moclei/motion-play/session_data/labeled-data/index.md

| session_id | label | ball_size |
|---|---|---|
|  device-001_19139_selection.csv | a_to_b_medium_edge | 4 inch |
| | | |

## Session location
Files named after the session_id are found in the group1 folder (session_data/labeled-data/group1)
