moclei/motion-play/docs/alt-design/motion-play-alt.rtf

Hoop Ball Detection System
Project Specification Document
Version 1.0 — December 2024
1. Project Overview
This project involves designing and building an electronics system that detects when a soccer ball passes through a suspended hoop, including the direction of travel. The system uses infrared beam-break detection with multiple sensor pairs to ensure reliable detection regardless of where the ball passes through the hoop's cross-section.
1.1 Functional Requirements
• Detect a soccer ball passing through the hoop
• Determine direction of travel (Side A → Side B or Side B → Side A)
• Operate reliably in various lighting conditions (indoor and outdoor)
• Battery-powered with USB-C charging capability
• Visual feedback via integrated display
2. Physical Specifications
2.1 Hoop Construction
Parameter | Value
Material | Flat bar steel
Bar dimensions | 25.4mm wide × 3.4mm thick × 1596mm long
Inner diameter | 500mm
Shape | Perfectly round (bent from flat stock)
Mounting height | Approximately 1 meter (suspended)
2.2 Ball Specifications
Parameter | Value
Type | Size 4 soccer ball
Diameter | 203mm
3. Detection System Design
3.1 Detection Method
The system uses infrared (IR) beam-break detection. IR LEDs emit 940nm light across the hoop diameter, and photodiodes on the opposite side detect the light. When a ball passes through, it blocks the beam, causing the photodiode output to change state.
3.2 Beam Geometry
With a 500mm hoop inner diameter and 203mm ball diameter, geometric analysis confirms that a minimum of three beams are required to guarantee detection regardless of where the ball passes through the hoop plane.
Beam positioning: Due to flex PCB manufacturing constraints (490mm maximum length at JLCPCB), an asymmetric arrangement is used rather than equal 120° spacing:
• IR LEDs positioned at: 0°, 50°, 100° on the hoop
• Sensor pairs positioned at: 180°, 230°, 280° (directly opposite)
• Arc span: 100° ≈ 436mm (within 490mm limit)
This arrangement has been verified geometrically: even at the worst-case position (140°), a ball will intersect at least one beam by approximately 6mm of its radius.
3.3 Direction Detection
Each beam position has two photodiode sensors spaced 25mm apart (the maximum achievable given hoop constraints). When a ball passes through:
1. The first sensor detects the beam break
2. Microseconds later, the second sensor detects the break
3. The order of detection determines direction of travel
The ESP32-S3 uses interrupt-driven timestamping to capture transitions with microsecond precision.
3.4 Timing Analysis
Ball transit times through the hoop plane (203mm travel distance):
Ball Speed | Transit Time | 25mm Sensor Gap
10 m/s (moderate kick) | 20.3ms | 2.5ms
20 m/s (hard kick) | 10.2ms | 1.25ms
30 m/s (professional) | 6.8ms | 0.83ms (833μs)
The selected photodiode (VEMD2020X01) has 100ns response time, providing approximately 8,300 sample opportunities during a 833μs sensor gap transit at maximum speed.
4. Component Selection
4.1 Microcontroller
Parameter | Specification
Module | LilyGO T-Display-S3
Processor | ESP32-S3
Display | Integrated TFT (visible during use)
Key features | Microsecond GPIO interrupt timestamping, multiple PWM channels
4.2 Power System
Parameter | Specification
Module | USB-C power module devkit
Input | USB-C
Output | 5V @ 2.4A via GPIO pins
Battery | 18650 cell (charges while providing power, auto-switchover)
4.3 IR Photodiode Sensors (PROTOTYPE)
Parameter | Specification
Part number | VEMD2020X01
LCSC Part # | C3210968
Manufacturer | Vishay
Type | Silicon PIN photodiode
Peak wavelength | 940nm
Spectral bandwidth | 750nm to 1050nm
Daylight filter | Yes — matched with 830nm to 950nm IR emitters
Half angle | ±15° (narrow, provides natural off-axis rejection)
Response time | 100ns rise/fall
Photocurrent | 12μA typical at 1mW/cm²
Package | 2.3mm × 2.3mm × 2.8mm SMD (gullwing)
Quantity required | 6 (2 per beam × 3 beams)
Stock (LCSC) | 12,235 units
Unit price | $0.364
Selection rationale: The VEMD2020X01 was selected over integrated IR receiver modules (like the IRM-V838M3-C) because those modules have AGC (automatic gain control) that requires burst timing patterns. The burst cycle (~1.2ms) is too slow for reliable direction detection at high ball speeds with 25mm sensor spacing. The photodiode's 100ns response time eliminates this constraint entirely.
4.4 IR LED Emitters (CANDIDATE — PENDING DATASHEET VERIFICATION)
Parameter | Specification
Part number | P2835P1VIRB8G025-940
LCSC Part # | C22466183
Manufacturer | Silverlight
Wavelength | 940nm
Half angle (estimated) | 12°-15°
Beam diameter at 500mm | ~106mm to ~134mm
Package | SMD, 3.5x2.8mm
Quantity required | 3 (1 per beam)
Stock (LCSC) | 230 units
Unit price | $0.1405
Status | Chosen for prototype
5. PCB Architecture
5.1 Board Configuration
The system uses three PCBs manufactured by JLCPCB:
4. Main PCB (rigid): Houses the T-Display-S3 MCU, USB-C power module, 18650 battery holder, ZIF FPC connectors, and supporting circuitry
5. LED Flex PCB: Contains 3× IR LEDs with drive circuits, spans 0° to 100° arc (~436mm)
6. Sensor Flex PCB: Contains 6× photodiodes with detection circuits, spans 180° to 280° arc (~436mm)
5.2 Flex PCB Connections
• ZIF FPC connectors on main PCB
• Flex PCBs conform to hoop's inner curve (250mm radius)
• SMD components only on flex PCBs (reliability on curved surface)
• 0.11mm or 0.2mm polyimide thickness for flexibility
• Stiffeners at component locations and connector ends
5.3 Signal Routing
LED Flex PCB signals: VCC, GND, PWM (can be shared for synchronized pulsing)
Sensor Flex PCB signals: VCC, GND, 6× sensor outputs (one per photodiode)
6. Mechanical Design
6.1 3D Printed Components
Custom 3D-printed clips attach to the 25.4mm × 3.4mm flat steel bar profile:
• Main enclosure clip: Houses main PCB, provides display visibility, battery access
• Flex PCB channel clips: Guide and protect flex PCBs along hoop interior
• Sensor housings: Position photodiodes with 25mm spacing, may include baffles if needed
• LED housings: Position and protect IR LEDs, ensure correct aiming
7. Open Items and Next Steps
7.1 Pending Tasks
7. Photodiode detection circuit design: Design transimpedance amplifier or comparator circuit for converting photodiode current to digital GPIO signal
8. LED drive circuit design: Size current-limiting resistors and MOSFET switches, determine continuous vs. pulsed operation
9. Schematic capture: Create KiCad schematics for all three PCBs
10. PCB layout: Layout main rigid PCB and both flex PCBs in KiCad
11. 3D enclosure design: Model mounting clips and enclosures
12. Firmware development: Implement interrupt-driven detection, direction logic, and display output
7.2 Design Decisions to Finalize
• Continuous vs. modulated (38kHz) LED drive — with photodiodes, continuous may be sufficient and simpler
• Photodiode bias mode — photovoltaic (simpler) vs. reverse-biased (faster, already fast enough)
• Detection circuit topology — simple resistive load vs. transimpedance amplifier vs. comparator
• Main PCB mounting position on hoop
— End of Document —
