moclei/motion-play/hardware/components/t-display-s3/Lilygo-T-display_s3_pinout.webp

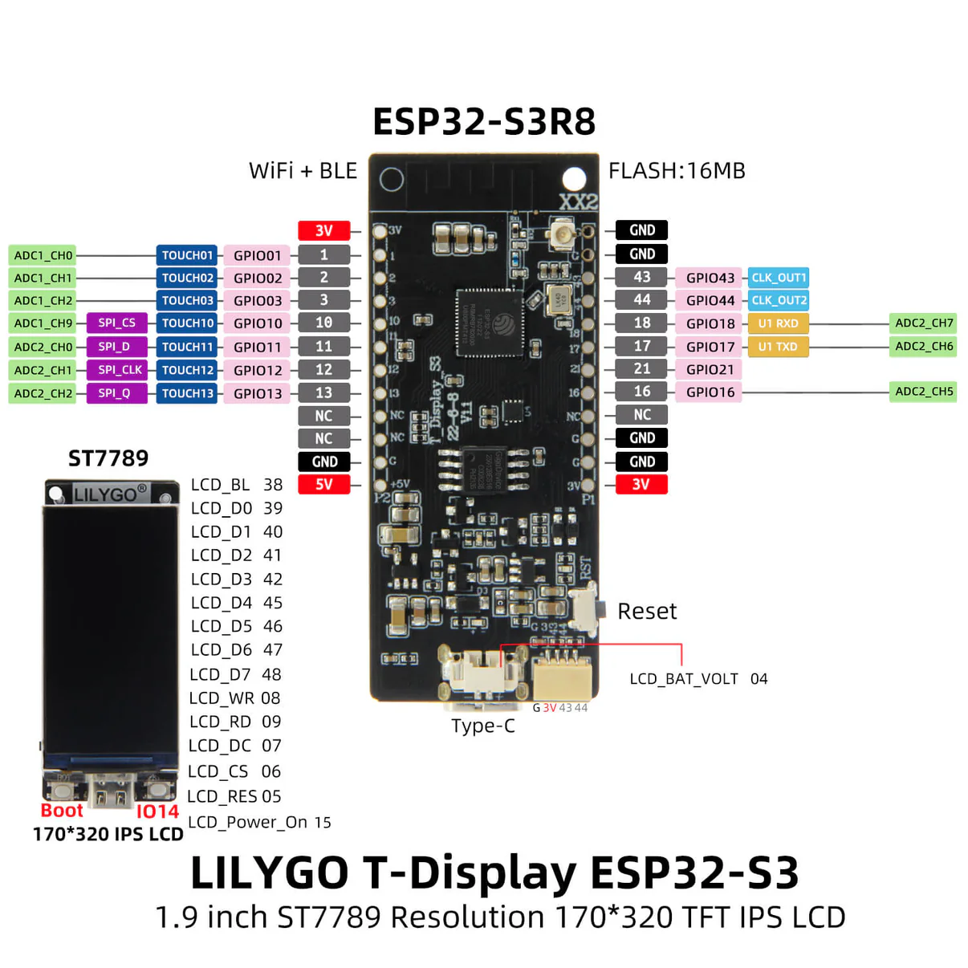
hardware/components/t-display-s3/Lilygo-T-display_s3_pinout.webp
