moclei/motion-play/hardware/components/dweii-power/product listing/Screenshot 2024-12-04 at 5.54.28 PM.png

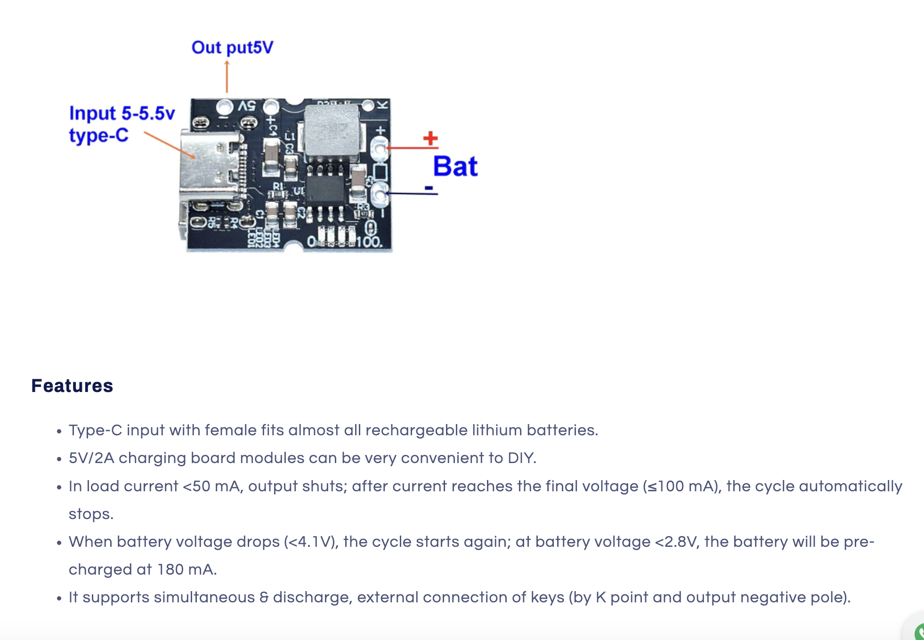
hardware/components/dweii-power/product listing/Screenshot 2024-12-04 at 5.54.28 PM.png
