moclei/motion-play/hardware/components/dweii-power/product listing/Screenshot 2024-12-04 at 5.56.42 PM.png

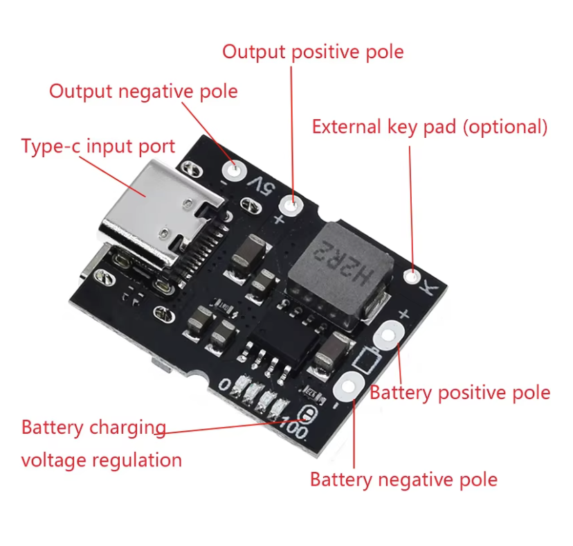
hardware/components/dweii-power/product listing/Screenshot 2024-12-04 at 5.56.42 PM.png
