moclei/motion-play/mechanical/models/router-template/pb_back_router_template_clean.dxf

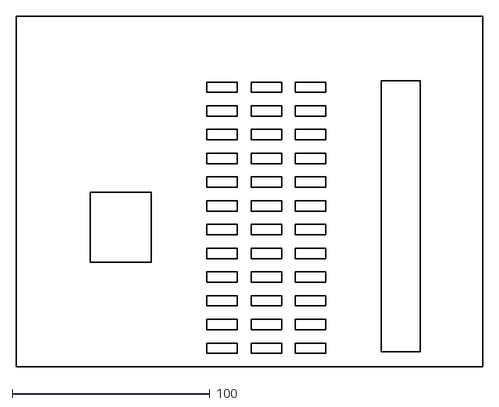
[picture p24: CAD file, 2026-04-03]
mechanical/models/router-template/pb_back_router_template_clean.dxf
235.8 x 177.1
