moclei/motion-play/hardware/components/TPS54331/TPS54331DR.step

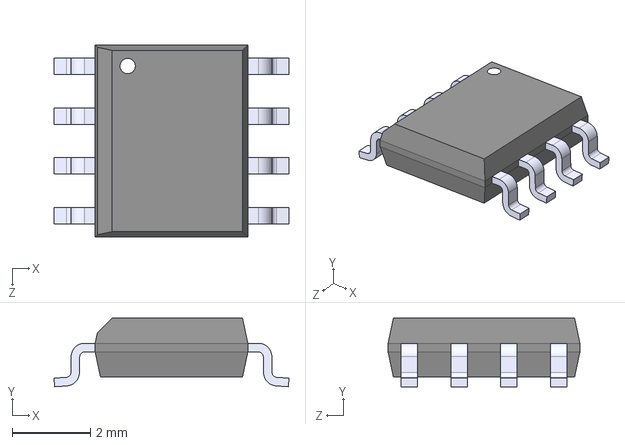
[picture p25: CAD file, 2025-09-09]
hardware/components/TPS54331/TPS54331DR.step
6.00 x 1.75 x 4.90 mm
