moclei/motion-play/hardware/pcb-power-supply/resources/BQ24195RGET/BQ24195RGET.step

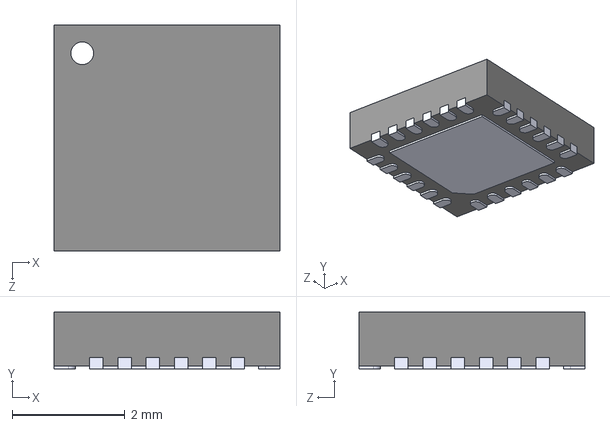
[picture p26: CAD file, 2025-09-03]
hardware/pcb-power-supply/resources/BQ24195RGET/BQ24195RGET.step
4.00 x 1.00 x 4.00 mm
