moclei/motion-play/hardware/components/tca9548a/reference schematic/Adafruit TCA9548A reference schematic.sch

## EAGLE design hardware/components/tca9548a/reference schematic/Adafruit TCA9548A reference schematic.sch (2025-09-03)


Parts:
A0, A1, A2: SOLDERJUMPER; SOLDERJUMPER_ARROW_NOPASTE
C1: 10uF; 0805-NO
FID1, FID3: FIDUCIAL""; FIDUCIAL_1MM
JP1, JP3: HEADER-1X12; 1X12_ROUND
R1, R2, R3, R4, R5: 10K; 0805-NO
R6: 10K; _0805MP
SCLPU: SOLDERJUMPERCLOSED; SOLDERJUMPER_CLOSEDWIRE
SDAPU: SOLDERJUMPERCLOSED; SOLDERJUMPER_CLOSEDWIRE
U1: TCA9548APWR; TSSOP24
U$4, U$5: MOUNTINGHOLE2.5; MOUNTINGHOLE_2.5_PLATED

Connections:
0SCL: JP3.10, U1.5 (SCL0)
0SDA: JP3.9, U1.4 (SDA0)
1SCL: JP3.12, U1.7 (SCL1)
1SDA: JP3.11, U1.6 (SDA1)
2SCL: JP1.2, U1.9 (SCL2)
2SDA: JP1.1, U1.8 (SDA2)
3SCL: JP1.4, U1.11 (SCL3)
3SDA: JP1.3, U1.10 (SDA3)
4SCL: JP1.6, U1.14 (SCL4)
4SDA: JP1.5, U1.13 (SDA4)
5SCL: JP1.8, U1.16 (SCL5)
5SDA: JP1.7, U1.15 (SDA5)
6SCL: JP1.10, U1.18 (SCL6)
6SDA: JP1.9, U1.17 (SDA6)
7SCL: JP1.12, U1.20 (SCL7)
7SDA: JP1.11, U1.19 (SDA7)
A0: A0.1, JP3.6, R5.1, U1.1 (A0)
A1: A1.1, JP3.7, R4.1, U1.2 (A1)
A2: A2.2, JP3.8, R3.1, U1.21 (A2)
GND: C1.2, JP3.2, R3.2, R4.2, R5.2, U1.12 (GND)
INPUTSCL: JP3.4, SCLPU.1, U1.22 (SCL)
INPUTSDA: JP3.3, SDAPU.1, U1.23 (SDA)
unnamed: R2.1, SCLPU.2
unnamed: R1.1, SDAPU.2
RESET: JP3.5, R6.1, U1.3 (#RESET)
VCC: A0.2, A1.2, A2.1, C1.1, JP3.1, R1.2, R2.2, R6.2, U1.24 (VCC)
