moclei/motion-play/firmware/src/components/data/DataTransmitter.cpp

#include "DataTransmitter.h"
#include "../memory/PSRAMAllocator.h"
#include "../calibration/CalibrationData.h"
#include "mbedtls/base64.h"

DataTransmitter::DataTransmitter(MQTTManager *mqtt) : mqttManager(mqtt)
{
    // Constructor
}

// ============================================================================
// Main entry point - routes to correct transmission method
// ============================================================================

bool DataTransmitter::transmitSession(SessionManager &session, const SensorConfiguration *config)
{
    if (session.getSessionType() == SessionType::INTERRUPT_BASED)
    {
        return transmitInterruptSession(session, config);
    }
    else
    {
        return transmitProximitySession(session, config);
    }
}

// ============================================================================
// Proximity Mode Transmission (existing implementation)
// ============================================================================

bool DataTransmitter::transmitBatch(const String &sessionId,
                                    const String &deviceId,
                                    unsigned long startTime,
                                    unsigned long duration,
                                    std::vector<SensorReading, PSRAMAllocator<SensorReading>> &readings,
                                    size_t offset,
                                    size_t count,
                                    const std::vector<SensorMetadata> *sensorMetadata,
                                    const SensorConfiguration *config)
{
    // Create JSON document
    DynamicJsonDocument doc(8192); // 8KB for batch

    doc["session_id"] = sessionId;
    doc["device_id"] = deviceId;
    doc["session_type"] = "proximity";           // Explicit session type
    doc["start_timestamp"] = startTime * 1000UL; // Convert session start from ms to us (consistent with reading timestamps)
    doc["duration_ms"] = duration;
    doc["sample_rate"] = SAMPLE_RATE_HZ;
    doc["batch_offset"] = offset;
    doc["batch_size"] = count;
    doc["timestamp_unit"] = "us"; // Signal to Lambda that timestamps are in microseconds

    // Add sensor metadata AND configuration (only in first batch)
    if (offset == 0 && sensorMetadata != nullptr)
    {
        // Add active sensor list
        JsonArray sensorArray = doc.createNestedArray("active_sensors");

        for (const auto &sensor : *sensorMetadata)
        {
            JsonObject sensorObj = sensorArray.createNestedObject();
            sensorObj["pos"] = sensor.position;
            sensorObj["pcb"] = sensor.pcb_id;
            sensorObj["side"] = sensor.side;
            sensorObj["name"] = sensor.name;
            sensorObj["active"] = sensor.active;
        }

        // Add VCNL4040 configuration parameters
        if (config != nullptr)
        {
            JsonObject configObj = doc.createNestedObject("vcnl4040_config");
            configObj["sample_rate_hz"] = config->sample_rate_hz;
            configObj["led_current"] = config->led_current;
            configObj["integration_time"] = config->integration_time;
            configObj["duty_cycle"] = config->duty_cycle;
            configObj["multi_pulse"] = config->multi_pulse;
            configObj["high_resolution"] = config->high_resolution;
            configObj["read_ambient"] = config->read_ambient;
            configObj["i2c_clock_khz"] = config->i2c_clock_khz;
            configObj["actual_sample_rate_hz"] = config->actual_sample_rate_hz;
        }

        // Add calibration metadata if available
        if (deviceCalibration.isValid())
        {
            JsonObject calObj = doc.createNestedObject("calibration");
            calObj["valid"] = true;
            calObj["timestamp"] = deviceCalibration.timestamp;
            calObj["multi_pulse"] = deviceCalibration.multi_pulse;
            calObj["integration_time"] = deviceCalibration.integration_time;

            JsonArray thresholds = calObj.createNestedArray("thresholds");
            for (int i = 0; i < CALIBRATION_NUM_PCBS; i++)
            {
                JsonObject pcbCal = thresholds.createNestedObject();
                pcbCal["pcb"] = i + 1;
                pcbCal["baseline_max"] = deviceCalibration.pcbs[i].baseline_max;
                pcbCal["signal_min"] = deviceCalibration.pcbs[i].signal_min;
                pcbCal["signal_max"] = deviceCalibration.pcbs[i].signal_max;
                pcbCal["threshold"] = deviceCalibration.pcbs[i].threshold;
            }
        }
        else
        {
            JsonObject calObj = doc.createNestedObject("calibration");
            calObj["valid"] = false;
        }
    }

    // Add readings array
    JsonArray readingsArray = doc.createNestedArray("readings");

    for (size_t i = 0; i < count; i++)
    {
        SensorReading &reading = readings[offset + i];

        JsonObject readingObj = readingsArray.createNestedObject();
        readingObj["ts"] = reading.timestamp_us;
        readingObj["pos"] = reading.position;
        readingObj["pcb"] = reading.pcb_id;
        readingObj["side"] = reading.side;
        readingObj["prox"] = reading.proximity;
        readingObj["amb"] = reading.ambient;
    }

    // Serialize to string
    String payload;
    size_t payloadSize = serializeJson(doc, payload);

    // Publish via MQTT (silent on success, only log errors)
    bool success = mqttManager->publishData(doc);

    if (!success)
    {
        Serial.println("ERROR: MQTT publish failed!");
        Serial.print("  Payload size: ");
        Serial.print(payloadSize);
        Serial.println(" bytes");
        Serial.print("  First 200 chars: ");
        Serial.println(payload.substring(0, 200));
    }
    else if (activeSummary)
    {
        // Session Confirmation: count transmitted readings and batches
        activeSummary->total_readings_transmitted += count;
        activeSummary->total_batches_transmitted++;
    }

    return success;
}

bool DataTransmitter::transmitProximitySession(SessionManager &session, const SensorConfiguration *config)
{
    if (!session.hasData())
    {
        Serial.println("No data to transmit");
        return false;
    }

    String sessionId = session.getSessionId();
    String deviceId = mqttManager->getDeviceId();
    unsigned long startTime = session.getStartTime();
    unsigned long duration = session.getDuration();

    std::vector<SensorReading, PSRAMAllocator<SensorReading>> &readings = session.getDataBuffer();
    const std::vector<SensorMetadata> &sensorMetadata = session.getSensorMetadata();
    size_t totalReadings = readings.size();

    Serial.print("Transmitting proximity session ");
    Serial.print(sessionId);
    Serial.print(" (");
    Serial.print(totalReadings);
    Serial.println(" readings)");

    // Send in batches
    size_t offset = 0;
    while (offset < totalReadings)
    {
        size_t remaining = totalReadings - offset;
        size_t batchCount = (remaining > BATCH_SIZE) ? BATCH_SIZE : remaining;

        // Pass sensor metadata and config only for first batch
        const std::vector<SensorMetadata> *metadataPtr = (offset == 0) ? &sensorMetadata : nullptr;
        const SensorConfiguration *configPtr = (offset == 0) ? config : nullptr;

        if (!transmitBatch(sessionId, deviceId, startTime, duration,
                           readings, offset, batchCount, metadataPtr, configPtr))
        {
            Serial.println("ERROR: Failed to transmit batch");
            return false;
        }

        offset += batchCount;

        // Small delay between batches to avoid overwhelming MQTT
        delay(100);
    }

    Serial.println("Proximity session transmission complete!");
    return true;
}

// ============================================================================
// Interrupt Mode Transmission (new implementation)
// ============================================================================

bool DataTransmitter::transmitInterruptBatch(const String &sessionId,
                                             const String &deviceId,
                                             unsigned long startTime,
                                             unsigned long duration,
                                             const std::vector<InterruptEvent> &events,
                                             size_t offset,
                                             size_t count,
                                             bool isFirstBatch,
                                             const SensorConfiguration *config)
{
    // Create JSON document
    DynamicJsonDocument doc(8192);

    doc["session_id"] = sessionId;
    doc["device_id"] = deviceId;
    doc["session_type"] = "interrupt"; // Explicit session type
    doc["start_timestamp"] = startTime;
    doc["duration_ms"] = duration;
    doc["batch_offset"] = offset;
    doc["batch_size"] = count;

    // Add interrupt configuration (only in first batch)
    // Uses calibration-based approach - thresholds are relative to auto-calibrated baseline
    if (isFirstBatch && config != nullptr)
    {
        JsonObject intConfig = doc.createNestedObject("interrupt_config");
        intConfig["threshold_margin"] = config->interrupt_threshold_margin;
        intConfig["hysteresis"] = config->interrupt_hysteresis;
        intConfig["integration_time"] = config->interrupt_integration_time;
        intConfig["multi_pulse"] = config->interrupt_multi_pulse;
        intConfig["persistence"] = config->interrupt_persistence;
        intConfig["smart_persistence"] = config->interrupt_smart_persistence;
        intConfig["mode"] = config->interrupt_mode;
        intConfig["led_current"] = config->led_current;

        // Add calibration metadata if available
        if (deviceCalibration.isValid())
        {
            JsonObject calObj = doc.createNestedObject("calibration");
            calObj["valid"] = true;
            calObj["timestamp"] = deviceCalibration.timestamp;
            calObj["multi_pulse"] = deviceCalibration.multi_pulse;
            calObj["integration_time"] = deviceCalibration.integration_time;

            JsonArray thresholds = calObj.createNestedArray("thresholds");
            for (int i = 0; i < CALIBRATION_NUM_PCBS; i++)
            {
                JsonObject pcbCal = thresholds.createNestedObject();
                pcbCal["pcb"] = i + 1;
                pcbCal["baseline_max"] = deviceCalibration.pcbs[i].baseline_max;
                pcbCal["signal_min"] = deviceCalibration.pcbs[i].signal_min;
                pcbCal["signal_max"] = deviceCalibration.pcbs[i].signal_max;
                pcbCal["threshold"] = deviceCalibration.pcbs[i].threshold;
            }
        }
        else
        {
            JsonObject calObj = doc.createNestedObject("calibration");
            calObj["valid"] = false;
        }
    }

    // Add events array
    JsonArray eventsArray = doc.createNestedArray("events");

    for (size_t i = 0; i < count; i++)
    {
        const InterruptEvent &evt = events[offset + i];

        JsonObject evtObj = eventsArray.createNestedObject();
        evtObj["ts"] = evt.timestamp_us;
        evtObj["board"] = evt.boardId;
        evtObj["sensor"] = evt.sensorId;

        // Convert event type to string
        switch (evt.type)
        {
        case InterruptEventType::CLOSE:
            evtObj["type"] = "close";
            break;
        case InterruptEventType::AWAY:
            evtObj["type"] = "away";
            break;
        default:
            evtObj["type"] = "unknown";
            break;
        }

        evtObj["flags"] = evt.rawFlags;
    }

    // Serialize to string for debugging
    String payload;
    size_t payloadSize = serializeJson(doc, payload);

    // Publish via MQTT
    bool success = mqttManager->publishData(doc);

    if (!success)
    {
        Serial.println("ERROR: MQTT publish failed for interrupt batch!");
        Serial.print("  Payload size: ");
        Serial.print(payloadSize);
        Serial.println(" bytes");
    }
    else
    {
        Serial.printf("  Sent interrupt batch: offset=%d, count=%d\n", offset, count);
    }

    return success;
}

bool DataTransmitter::transmitInterruptSession(SessionManager &session, const SensorConfiguration *config)
{
    if (!session.hasData())
    {
        Serial.println("No interrupt events to transmit");
        return false;
    }

    String sessionId = session.getSessionId();
    String deviceId = mqttManager->getDeviceId();
    unsigned long startTime = session.getStartTime();
    unsigned long duration = session.getDuration();

    const std::vector<InterruptEvent> &events = session.getInterruptBuffer();
    size_t totalEvents = events.size();

    Serial.print("Transmitting interrupt session ");
    Serial.print(sessionId);
    Serial.print(" (");
    Serial.print(totalEvents);
    Serial.println(" events)");

    // Send in batches (interrupt events are smaller, can send more per batch)
    size_t offset = 0;
    while (offset < totalEvents)
    {
        size_t remaining = totalEvents - offset;
        size_t batchCount = (remaining > INT_BATCH_SIZE) ? INT_BATCH_SIZE : remaining;

        bool isFirstBatch = (offset == 0);

        if (!transmitInterruptBatch(sessionId, deviceId, startTime, duration,
                                    events, offset, batchCount, isFirstBatch, config))
        {
            Serial.println("ERROR: Failed to transmit interrupt batch");
            return false;
        }

        offset += batchCount;

        // Small delay between batches
        delay(50);
    }

    Serial.println("Interrupt session transmission complete!");
    return true;
}

// ============================================================================
// Live Debug Capture Transmission
// ============================================================================

String DataTransmitter::transmitLiveDebugCapture(
    std::vector<SensorReading, PSRAMAllocator<SensorReading>> &readings,
    size_t startIdx,
    size_t count,
    const char *captureReason,
    const char *detectionDirection,
    float detectionConfidence,
    const SensorConfiguration *config)
{
    if (count == 0)
    {
        Serial.println("Live Debug: No readings to transmit");
        return "";
    }

    // Generate a unique session ID for this capture
    String deviceId = mqttManager->getDeviceId();
    // Extract short device suffix for session ID (e.g. "motionplay-device-002" -> "device-002")
    String deviceSuffix = deviceId;
    int lastDash = deviceId.lastIndexOf('-');
    int secondLastDash = deviceId.lastIndexOf('-', lastDash - 1);
    if (secondLastDash >= 0)
    {
        deviceSuffix = deviceId.substring(secondLastDash + 1);
    }
    String sessionId = deviceSuffix + "_" + String(millis());

    // Calculate timing from the readings themselves (timestamps are in microseconds)
    unsigned long startTime = readings[startIdx].timestamp_us;
    unsigned long endTime = readings[startIdx + count - 1].timestamp_us;
    unsigned long durationUs = endTime - startTime;
    unsigned long durationMs = durationUs / 1000;

    Serial.printf("Live Debug capture: reason=%s, readings=%d, duration=%lums\n",
                  captureReason, count, durationMs);

    // Send in batches using Live Debug batch settings
    size_t offset = 0;
    while (offset < count)
    {
        size_t remaining = count - offset;
        size_t batchCount = (remaining > LIVE_DEBUG_BATCH_SIZE) ? LIVE_DEBUG_BATCH_SIZE : remaining;

        // Create JSON document — 32KB to comfortably fit 200 readings
        // At ~80 bytes per reading in ArduinoJson memory, 200 readings needs ~16KB+
        // Previous 16KB buffer silently truncated readings via ArduinoJson overflow
        DynamicJsonDocument doc(32768);

        doc["session_id"] = sessionId;
        doc["device_id"] = deviceId;
        doc["session_type"] = "proximity";
        doc["mode"] = "live_debug";
        doc["start_timestamp"] = startTime; // Microseconds (first reading timestamp)
        doc["duration_ms"] = durationMs;
        doc["timestamp_unit"] = "us"; // Signal to Lambda that timestamps are in microseconds
        doc["sample_rate"] = SAMPLE_RATE_HZ;
        doc["batch_offset"] = offset;
        doc["batch_size"] = batchCount;

        // First batch: include capture metadata and config
        if (offset == 0)
        {
            // Live Debug capture metadata
            doc["capture_reason"] = captureReason;
            if (detectionDirection != nullptr)
            {
                doc["detection_direction"] = detectionDirection;
                doc["detection_confidence"] = detectionConfidence;
            }

            // Sensor configuration
            if (config != nullptr)
            {
                JsonObject configObj = doc.createNestedObject("vcnl4040_config");
                configObj["sample_rate_hz"] = config->sample_rate_hz;
                configObj["led_current"] = config->led_current;
                configObj["integration_time"] = config->integration_time;
                configObj["duty_cycle"] = config->duty_cycle;
                configObj["multi_pulse"] = config->multi_pulse;
                configObj["high_resolution"] = config->high_resolution;
                configObj["read_ambient"] = config->read_ambient;
                configObj["i2c_clock_khz"] = config->i2c_clock_khz;
                configObj["actual_sample_rate_hz"] = config->actual_sample_rate_hz;
            }

            // Calibration metadata
            if (deviceCalibration.isValid())
            {
                JsonObject calObj = doc.createNestedObject("calibration");
                calObj["valid"] = true;
                calObj["timestamp"] = deviceCalibration.timestamp;
                calObj["multi_pulse"] = deviceCalibration.multi_pulse;
                calObj["integration_time"] = deviceCalibration.integration_time;

                JsonArray thresholds = calObj.createNestedArray("thresholds");
                for (int i = 0; i < CALIBRATION_NUM_PCBS; i++)
                {
                    JsonObject pcbCal = thresholds.createNestedObject();
                    pcbCal["pcb"] = i + 1;
                    pcbCal["baseline_max"] = deviceCalibration.pcbs[i].baseline_max;
                    pcbCal["signal_min"] = deviceCalibration.pcbs[i].signal_min;
                    pcbCal["signal_max"] = deviceCalibration.pcbs[i].signal_max;
                    pcbCal["threshold"] = deviceCalibration.pcbs[i].threshold;
                }
            }
        }

        // Add readings array
        JsonArray readingsArray = doc.createNestedArray("readings");
        for (size_t i = 0; i < batchCount; i++)
        {
            SensorReading &reading = readings[startIdx + offset + i];

            JsonObject readingObj = readingsArray.createNestedObject();
            readingObj["ts"] = reading.timestamp_us;
            readingObj["pos"] = reading.position;
            readingObj["pcb"] = reading.pcb_id;
            readingObj["side"] = reading.side;
            readingObj["prox"] = reading.proximity;
            readingObj["amb"] = reading.ambient;
        }

        // Check for ArduinoJson buffer overflow (silent data truncation)
        size_t actualReadingsInDoc = readingsArray.size();
        if (doc.overflowed())
        {
            Serial.printf("WARNING: ArduinoJson overflow! Wanted %d readings, only %d fit (doc: %d/%d bytes)\n",
                          batchCount, actualReadingsInDoc, doc.memoryUsage(), 32768);
        }

        // Publish via MQTT
        bool success = mqttManager->publishData(doc);
        if (!success)
        {
            String payload;
            size_t payloadSize = serializeJson(doc, payload);
            Serial.printf("ERROR: Live Debug MQTT publish failed! Size: %d bytes\n", payloadSize);
            return "";
        }

        // Session Confirmation: count only readings that actually made it into the JSON
        if (activeSummary)
        {
            activeSummary->total_readings_transmitted += actualReadingsInDoc;
            activeSummary->total_batches_transmitted++;
        }

        offset += batchCount;

        // Short delay between batches
        if (offset < count)
        {
            delay(LIVE_DEBUG_BATCH_DELAY);
        }
    }

    uint32_t actualTransmitted = activeSummary ? activeSummary->total_readings_transmitted : count;
    Serial.printf("Live Debug capture transmitted: session=%s, %d/%d readings in %d batches\n",
                  sessionId.c_str(), actualTransmitted, count,
                  activeSummary ? activeSummary->total_batches_transmitted : 0);
    return sessionId;
}

// ============================================================================
// Live Debug Capture — Binary-Packed Single Message
// ============================================================================

String DataTransmitter::transmitLiveDebugCaptureBinary(
    std::vector<SensorReading, PSRAMAllocator<SensorReading>> &readings,
    size_t startIdx,
    size_t count,
    const char *captureReason,
    const char *detectionDirection,
    float detectionConfidence,
    const SessionSummary &summary,
    const SensorConfiguration *config)
{
    if (count == 0)
    {
        Serial.println("Live Debug Binary: No readings to transmit");
        return "";
    }

    // Generate session ID
    String deviceId = mqttManager->getDeviceId();
    String deviceSuffix = deviceId;
    int lastDash = deviceId.lastIndexOf('-');
    int secondLastDash = deviceId.lastIndexOf('-', lastDash - 1);
    if (secondLastDash >= 0)
    {
        deviceSuffix = deviceId.substring(secondLastDash + 1);
    }
    String sessionId = deviceSuffix + "_" + String(millis());

    // Calculate timing from the readings themselves (timestamps are in microseconds)
    unsigned long startTime = readings[startIdx].timestamp_us;
    unsigned long endTime = readings[startIdx + count - 1].timestamp_us;
    unsigned long durationUs = endTime - startTime;
    unsigned long durationMs = durationUs / 1000;

    Serial.printf("Live Debug Binary: reason=%s, readings=%d, duration=%lums\n",
                  captureReason, count, durationMs);

    // 1. Pack readings into binary buffer (9 bytes per reading, little-endian)
    size_t binarySize = count * 9;
    uint8_t *binaryBuf = (uint8_t *)ps_malloc(binarySize);
    if (!binaryBuf)
    {
        Serial.printf("ERROR: Failed to allocate %d bytes in PSRAM for binary buffer\n", binarySize);
        return "";
    }

    for (size_t i = 0; i < count; i++)
    {
        SensorReading &r = readings[startIdx + i];
        size_t off = i * 9;
        memcpy(binaryBuf + off, &r.timestamp_us, 4);
        binaryBuf[off + 4] = r.position;
        memcpy(binaryBuf + off + 5, &r.proximity, 2);
        memcpy(binaryBuf + off + 7, &r.ambient, 2);
    }

    // 2. Base64-encode
    size_t base64Len = 0;
    mbedtls_base64_encode(NULL, 0, &base64Len, binaryBuf, binarySize);

    unsigned char *base64Buf = (unsigned char *)ps_malloc(base64Len + 1);
    if (!base64Buf)
    {
        Serial.printf("ERROR: Failed to allocate %d bytes in PSRAM for base64 buffer\n", base64Len + 1);
        free(binaryBuf);
        return "";
    }

    size_t written = 0;
    mbedtls_base64_encode(base64Buf, base64Len + 1, &written, binaryBuf, binarySize);
    base64Buf[written] = '\0';
    free(binaryBuf);

    Serial.printf("Live Debug Binary: packed %d bytes -> %d bytes base64\n", binarySize, written);

    // 3. Build JSON document
    // ArduinoJson stores char* by reference (zero-copy), so the doc only needs
    // memory for the JSON structure itself, not the base64 string content.
    DynamicJsonDocument doc(8192);

    // Session metadata
    doc["session_id"] = sessionId;
    doc["device_id"] = deviceId;
    doc["session_type"] = "proximity";
    doc["mode"] = "live_debug";
    doc["start_timestamp"] = startTime;
    doc["duration_ms"] = durationMs;
    doc["timestamp_unit"] = "us";
    doc["sample_rate"] = SAMPLE_RATE_HZ;

    // Capture metadata
    doc["capture_reason"] = captureReason;
    if (detectionDirection != nullptr)
    {
        doc["detection_direction"] = detectionDirection;
        doc["detection_confidence"] = detectionConfidence;
    }

    // Binary reading payload
    doc["reading_format"] = "bin9";
    doc["reading_count"] = count;
    doc["readings_b64"] = (const char *)base64Buf;

    // Sensor configuration
    if (config != nullptr)
    {
        JsonObject configObj = doc.createNestedObject("vcnl4040_config");
        configObj["sample_rate_hz"] = config->sample_rate_hz;
        configObj["led_current"] = config->led_current;
        configObj["integration_time"] = config->integration_time;
        configObj["duty_cycle"] = config->duty_cycle;
        configObj["multi_pulse"] = config->multi_pulse;
        configObj["high_resolution"] = config->high_resolution;
        configObj["read_ambient"] = config->read_ambient;
        configObj["i2c_clock_khz"] = config->i2c_clock_khz;
        configObj["actual_sample_rate_hz"] = config->actual_sample_rate_hz;
    }

    // Calibration metadata
    if (deviceCalibration.isValid())
    {
        JsonObject calObj = doc.createNestedObject("calibration");
        calObj["valid"] = true;
        calObj["timestamp"] = deviceCalibration.timestamp;
        calObj["multi_pulse"] = deviceCalibration.multi_pulse;
        calObj["integration_time"] = deviceCalibration.integration_time;

        JsonArray thresholds = calObj.createNestedArray("thresholds");
        for (int i = 0; i < CALIBRATION_NUM_PCBS; i++)
        {
            JsonObject pcbCal = thresholds.createNestedObject();
            pcbCal["pcb"] = i + 1;
            pcbCal["baseline_max"] = deviceCalibration.pcbs[i].baseline_max;
            pcbCal["signal_min"] = deviceCalibration.pcbs[i].signal_min;
            pcbCal["signal_max"] = deviceCalibration.pcbs[i].signal_max;
            pcbCal["threshold"] = deviceCalibration.pcbs[i].threshold;
        }
    }

    // Inline session summary — Lambda processes everything in one shot
    doc["type"] = "session_summary";
    JsonObject summaryObj = doc.createNestedObject("summary");
    summaryObj["total_cycles"] = summary.total_cycles;
    summaryObj["queue_drops"] = summary.queue_drops;
    summaryObj["buffer_drops"] = summary.buffer_drops;
    summaryObj["total_readings_transmitted"] = count;
    summaryObj["total_batches_transmitted"] = 1;
    summaryObj["measured_cycle_rate_hz"] = summary.measured_cycle_rate_hz;
    summaryObj["duration_ms"] = summary.duration_ms;
    summaryObj["theoretical_max_readings"] = summary.theoretical_max_readings;
    summaryObj["num_active_sensors"] = summary.num_active_sensors;

    JsonArray collectedArr = summaryObj.createNestedArray("readings_collected");
    JsonArray errorsArr = summaryObj.createNestedArray("i2c_errors");
    for (int i = 0; i < NUM_SENSORS; i++)
    {
        collectedArr.add(summary.readings_collected[i]);
        errorsArr.add(summary.i2c_errors[i]);
    }

    if (doc.overflowed())
    {
        Serial.printf("ERROR: JSON doc overflow! (usage=%d/8192 bytes)\n", doc.memoryUsage());
        free(base64Buf);
        return "";
    }

    // 4. Publish via streaming API (payload exceeds the 32KB PubSubClient buffer)
    bool success = mqttManager->publishDataStreaming(doc);
    free(base64Buf);

    if (!success)
    {
        Serial.println("ERROR: Live Debug Binary MQTT streaming publish failed!");
        return "";
    }

    Serial.printf("Live Debug Binary: session=%s, %d readings in 1 message\n",
                  sessionId.c_str(), count);
    return sessionId;
}

// ============================================================================
// Session Confirmation: Transmit pipeline integrity summary
// ============================================================================

bool DataTransmitter::transmitSessionSummary(const SessionSummary &summary,
                                             const String &sessionId,
                                             const String &deviceId)
{
    DynamicJsonDocument doc(4096);

    doc["type"] = "session_summary";
    doc["session_id"] = sessionId;
    doc["device_id"] = deviceId;

    JsonObject summaryObj = doc.createNestedObject("summary");
    summaryObj["total_cycles"] = summary.total_cycles;
    summaryObj["queue_drops"] = summary.queue_drops;
    summaryObj["buffer_drops"] = summary.buffer_drops;
    summaryObj["total_readings_transmitted"] = summary.total_readings_transmitted;
    summaryObj["total_batches_transmitted"] = summary.total_batches_transmitted;
    summaryObj["measured_cycle_rate_hz"] = summary.measured_cycle_rate_hz;
    summaryObj["duration_ms"] = summary.duration_ms;
    summaryObj["theoretical_max_readings"] = summary.theoretical_max_readings;
    summaryObj["num_active_sensors"] = summary.num_active_sensors;

    // Per-sensor arrays
    JsonArray collectedArr = summaryObj.createNestedArray("readings_collected");
    JsonArray errorsArr = summaryObj.createNestedArray("i2c_errors");
    for (int i = 0; i < NUM_SENSORS; i++)
    {
        collectedArr.add(summary.readings_collected[i]);
        errorsArr.add(summary.i2c_errors[i]);
    }

    // Retry up to 3 times
    for (int attempt = 0; attempt < 3; attempt++)
    {
        if (mqttManager->publishData(doc))
        {
            Serial.printf("Session summary transmitted (attempt %d)\n", attempt + 1);
            return true;
        }
        Serial.printf("WARNING: Session summary publish failed (attempt %d/3)\n", attempt + 1);
        delay(500);
    }

    Serial.println("ERROR: Failed to transmit session summary after 3 attempts");
    return false;
}
