moclei/motion-play/firmware/src/components/detection/DirectionDetector.h

#ifndef DIRECTION_DETECTOR_H
#define DIRECTION_DETECTOR_H

#include <Arduino.h>
#include <vector>
#include "../sensor/SensorManager.h"
#include "../calibration/CalibrationData.h"

/**
 * Direction Detection - Version 4: Per-Sensor Adaptive Thresholds
 *
 * Each of the 6 sensors tracks independently with its own rolling baseline
 * and adaptive threshold. Detection works in three layers:
 *
 * Layer 1 - Per-Sensor: Each sensor maintains a rolling baseline (only updated
 *   during IDLE — transit waves are excluded), computes its own adaptive
 *   threshold, and runs an independent wave state machine.
 *
 * Layer 2 - Per-Module: When both sensors on a module complete waves within
 *   a valid time window, that module produces a detection with direction
 *   from center-of-mass comparison.
 *
 * Layer 3 - Consensus: Multiple modules detecting the same direction boosts
 *   confidence. Disagreement lowers it.
 */

enum class Direction
{
    UNKNOWN,
    A_TO_B,
    B_TO_A
};

enum class DetectorState
{
    ESTABLISHING_BASELINE,
    READY,
    DETECTING
};

enum class WaveState
{
    IDLE,
    IN_WAVE,
    COMPLETE
};

struct DetectionResult
{
    Direction direction;
    float confidence;
    uint32_t centerOfMassA;
    uint32_t centerOfMassB;
    uint32_t comGapMs;
    uint16_t maxSignalA;
    uint16_t maxSignalB;
    uint32_t waveDurationA;
    uint32_t waveDurationB;
    float baselineA;
    float baselineB;
    float thresholdA;
    float thresholdB;
    uint8_t detectedModule;  // 1-3 for which module triggered, 0 for none
    uint8_t modulesDetected; // how many modules corroborated
};

struct DetectorConfig
{
    uint16_t baselineReadings = 50;
    float peakMultiplier = 1.5f;
    uint16_t minRise = 10;

    uint8_t smoothingWindow = 5;
    uint32_t minWaveDurationMs = 8;
    uint32_t maxWaveDurationMs = 200;
    uint32_t maxPeakGapMs = 150;
    float waveExitThreshold = 0.5f;

    uint32_t minGapForConfidence = 5;
    float minSignalForConfidence = 20;
};

/**
 * Ring buffer for smoothing and baseline tracking
 */
template <typename T, size_t SIZE>
class RingBuffer
{
private:
    T buffer[SIZE];
    size_t head = 0;
    size_t count = 0;

public:
    void push(const T &item)
    {
        buffer[head] = item;
        head = (head + 1) % SIZE;
        if (count < SIZE)
            count++;
    }

    T &operator[](size_t idx)
    {
        size_t actualIdx = (head - count + idx + SIZE) % SIZE;
        return buffer[actualIdx];
    }

    const T &operator[](size_t idx) const
    {
        size_t actualIdx = (head - count + idx + SIZE) % SIZE;
        return buffer[actualIdx];
    }

    size_t size() const { return count; }
    void clear()
    {
        count = 0;
        head = 0;
    }
    bool isFull() const { return count == SIZE; }

    float getSmoothedAverage(size_t windowSize) const
    {
        if (count == 0)
            return 0;
        size_t n = min(windowSize, count);
        float sum = 0;
        for (size_t i = count - n; i < count; i++)
        {
            sum += buffer[(head - count + i + SIZE) % SIZE];
        }
        return sum / n;
    }

    float getMax() const
    {
        if (count == 0)
            return 0;
        float maxVal = buffer[(head - count + SIZE) % SIZE];
        for (size_t i = 1; i < count; i++)
        {
            float val = buffer[(head - count + i + SIZE) % SIZE];
            if (val > maxVal)
                maxVal = val;
        }
        return maxVal;
    }
};

/**
 * Independent tracker for a single sensor.
 * Maintains its own baseline, threshold, and wave state.
 */
struct SensorTracker
{
    static const size_t SMOOTH_SIZE = 10;
    static const size_t BASELINE_SIZE = 200;

    RingBuffer<float, SMOOTH_SIZE> smoothBuffer;
    RingBuffer<float, BASELINE_SIZE> baselineBuffer;
    uint32_t baselineUpdateCount = 0;
    bool baselineReady = false;

    float threshold = 0;

    WaveState waveState = WaveState::IDLE;
    uint32_t waveStartTime = 0;
    uint32_t waveEndTime = 0;
    uint32_t peakTime = 0;
    float peakValue = 0;
    float weightedSum = 0;
    float totalWeight = 0;
    uint32_t centerOfMass = 0;

    void resetWave()
    {
        waveState = WaveState::IDLE;
        waveStartTime = 0;
        waveEndTime = 0;
        peakTime = 0;
        peakValue = 0;
        weightedSum = 0;
        totalWeight = 0;
        centerOfMass = 0;
    }

    void fullReset()
    {
        smoothBuffer.clear();
        baselineBuffer.clear();
        baselineUpdateCount = 0;
        baselineReady = false;
        threshold = 0;
        resetWave();
    }
};

class DirectionDetector
{
private:
    DetectorConfig config;
    SensorTracker sensors[NUM_SENSORS];

    const DeviceCalibration *_calibration = nullptr;
    bool _useCalibration = false;

    // Tracks which module last produced a detection (for telemetry)
    int _detectedModule = -1;

    void updateSensorWave(SensorTracker &sensor, float smoothed, uint32_t timestamp);
    void recalculateThreshold(SensorTracker &sensor, uint8_t position);
    bool isModuleDetected(int module) const;

public:
    DirectionDetector();
    DirectionDetector(const DetectorConfig &cfg);

    void addReading(const SensorReading &reading);
    void flushReading();

    bool hasDetection() const;
    DetectionResult getResult();

    void reset();
    void fullReset();

    bool isReady() const;
    DetectorState getState() const;

    void setConfig(const DetectorConfig &cfg);
    void setCalibration(const DeviceCalibration *cal);
    bool isUsingCalibration() const { return _useCalibration; }

    // Per-sensor telemetry accessors
    float getSensorThreshold(uint8_t position) const;
    float getSensorSmoothed(uint8_t position) const;
    WaveState getSensorWaveState(uint8_t position) const;

    // Legacy telemetry (returns data from most recently detected module, or module 0)
    float getSmoothedA() const;
    float getSmoothedB() const;
    float getThresholdA() const;
    float getThresholdB() const;
    WaveState getWaveStateA() const;
    WaveState getWaveStateB() const;

    static const char *directionToString(Direction dir);
    void debugPrint() const;
};

#endif
