moclei/motion-play/firmware/src/components/serialstudio/SerialStudioOutput.h

#ifndef SERIAL_STUDIO_OUTPUT_H
#define SERIAL_STUDIO_OUTPUT_H

#include <Arduino.h>
#include "../sensor/SensorManager.h"
#include "../sensor/SensorConfiguration.h"
#include "../detection/DirectionDetector.h"
#include "../memory/PSRAMAllocator.h"

class SerialStudioOutput
{
private:
    // Reference to the session data buffer (owned by SessionManager)
    std::vector<SensorReading, PSRAMAllocator<SensorReading>> *_buffer = nullptr;
    DirectionDetector *_detector = nullptr;
    SensorConfiguration *_config = nullptr;
    bool _enabled = false;
    bool _emitTelemetry = false;

    // Buffer read tracking
    size_t _lastProcessedIndex = 0;

    // Frame accumulator: one slot per sensor position (0-5)
    uint16_t _accumulator[NUM_SENSORS] = {0};
    bool _slotFilled[NUM_SENSORS] = {false};
    uint32_t _currentTimestamp = 0;
    bool _hasPendingFrame = false;

    // Detection result cache (persists until next detection or full reset)
    Direction _cachedDirection = Direction::UNKNOWN;
    float _cachedConfidence = 0.0f;
    float _cachedSpeedMs = 0.0f; // Estimated transit speed in m/s
    uint16_t _cachedPeakA = 0;
    uint16_t _cachedPeakB = 0;
    uint32_t _cachedWaveDurA = 0;
    uint32_t _cachedWaveDurB = 0;
    uint32_t _cachedComGap = 0;
    uint8_t _cachedDetModule = 0; // 1-3 for module, 0 for none

    // Rate tracking
    uint32_t _pollCount = 0;         // Frames emitted in current 1-second window
    unsigned long _rateWindowStart = 0;
    uint16_t _pollRate = 0;          // Measured I2C polling rate (cycles/sec)
    uint16_t _sensorRate = 0;        // Calculated sensor measurement rate (Hz) from IT × duty

    uint16_t calculateSensorRate();
    void emitFrame();
    void resetAccumulator(uint32_t newTimestamp);

public:
    /**
     * Initialize with references to session data buffer and direction detector.
     */
    void begin(std::vector<SensorReading, PSRAMAllocator<SensorReading>> *buffer,
               DirectionDetector *detector);

    void setEnabled(bool enabled) { _enabled = enabled; }
    bool isEnabled() const { return _enabled; }

    void setConfig(SensorConfiguration *config) { _config = config; }

    /**
     * When true, frames include algorithm telemetry fields (smoothed signals,
     * thresholds, wave states, detection status). Set to true in PLAY/LIVE_DEBUG.
     */
    void setEmitTelemetry(bool emit) { _emitTelemetry = emit; }

    /**
     * Cache a detection result so it persists in the output after the detector
     * is reset. Remains until the next detection or a full reset.
     */
    void cacheDetection(const DetectionResult &result);

    /**
     * Process new readings from the buffer and emit CSV frames.
     * Call once per Core 1 loop iteration, after sessionManager.processQueue().
     */
    void update();

    /**
     * Reset read index and accumulator state.
     * Call when the buffer is cleared externally (detection events, overflow).
     */
    void resetIndex();
};

#endif
