moclei/motion-play/firmware/src/components/network/NetworkManager.h

#ifndef NETWORK_MANAGER_H
#define NETWORK_MANAGER_H

#include <WiFi.h>
#include <WiFiClientSecure.h>
#include <ArduinoJson.h>
#include <LittleFS.h>

class NetworkManager {
private:
    String ssid;
    String password;
    String deviceId;
    String apiEndpoint;
    WiFiClientSecure wifiClient;
    bool connected = false;

public:
    NetworkManager();
    bool loadConfig();
    bool connectWiFi();
    void disconnect();
    bool isConnected();
    WiFiClientSecure& getClient();
    void checkConnection();
    String getDeviceId();
    String getApiEndpoint();
};

#endif
