moclei/motion-play/firmware/src/led_strip_test.cpp

/**
 * Motion Play - LED Strip Test
 *
 * Simple test program to verify WS2812B/WS2818B LED strip functionality
 *
 * Hardware:
 * - T-Display-S3 (ESP32-S3)
 * - WS2818B addressable LED strip (72 LEDs)
 * - Signal on GPIO 16 through SN74AHCT125 logic level shifter
 *
 * This test program will:
 * - Initialize the LED strip
 * - Display a nice red color on all LEDs
 * - Show status on the built-in display
 */

#include <Arduino.h>
#include <FastLED.h>
#include <TFT_eSPI.h>
#include "pin_config.h"

// LED Strip Configuration
#define NUM_LEDS 72
#define LED_TYPE WS2812B
#define COLOR_ORDER GRB
#define BRIGHTNESS 128 // 0-255, starting at 50% brightness for safety

// Create LED array
CRGB leds[NUM_LEDS];

// Display
TFT_eSPI tft = TFT_eSPI();

// Colors for testing
const CRGB COLOR_RED = CRGB::Red;
const CRGB COLOR_GREEN = CRGB::Green;
const CRGB COLOR_BLUE = CRGB::Blue;
const CRGB COLOR_YELLOW = CRGB::Yellow;
const CRGB COLOR_PURPLE = CRGB::Purple;
const CRGB COLOR_CYAN = CRGB::Cyan;
const CRGB COLOR_WHITE = CRGB::White;
const CRGB COLOR_OFF = CRGB::Black;

void initDisplay()
{
    // Power on display
    pinMode(PIN_POWER_ON, OUTPUT);
    digitalWrite(PIN_POWER_ON, HIGH);

    // Initialize TFT
    tft.init();
    tft.setRotation(1); // Landscape
    tft.fillScreen(TFT_BLACK);
    tft.setTextColor(TFT_WHITE, TFT_BLACK);
    tft.setTextSize(2);

    // Draw header
    tft.setCursor(10, 10);
    tft.println("Motion Play");
    tft.setCursor(10, 30);
    tft.println("LED Strip Test");
    tft.drawLine(0, 50, tft.width(), 50, TFT_CYAN);
}

void displayStatus(const char *message, uint16_t color = TFT_WHITE)
{
    static int lineNum = 0;
    int yPos = 60 + (lineNum * 20);

    if (yPos > tft.height() - 30)
    {
        // Clear status area when full
        tft.fillRect(0, 60, tft.width(), tft.height() - 60, TFT_BLACK);
        lineNum = 0;
        yPos = 60;
    }

    tft.setTextColor(color, TFT_BLACK);
    tft.setCursor(10, yPos);
    tft.println(message);
    lineNum++;
}

void initLEDStrip()
{
    // Add LED strip configuration
    FastLED.addLeds<LED_TYPE, PIN_LED_STRIP_DATA, COLOR_ORDER>(leds, NUM_LEDS);

    // Set master brightness control
    FastLED.setBrightness(BRIGHTNESS);

    // Clear all LEDs to start
    FastLED.clear();
    FastLED.show();

    Serial.println("LED strip initialized");
    Serial.printf("  Type: WS2818B/WS2812B\n");
    Serial.printf("  Count: %d LEDs\n", NUM_LEDS);
    Serial.printf("  Data Pin: GPIO %d\n", PIN_LED_STRIP_DATA);
    Serial.printf("  Brightness: %d/255\n", BRIGHTNESS);
}

void setAllLEDs(CRGB color)
{
    fill_solid(leds, NUM_LEDS, color);
    FastLED.show();
}
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
